MaximilianHq/bsc-thesis-agv-autonomous-parking/AGV/AGV CODE/src/MCU1/lift.h

#pragma once
#include <Arduino.h>
#include "system_actions.h"
#include <types.h>
#include <servo_continious.h>

class AGVCtrl;

class Lift
{
public:
    Lift(int pin_servo, int pin_begin_stop, int pin_endstop,
         int pwm_chnl, bool invert)
        : _servo(pin_servo, pwm_chnl, invert),
          _pin_begin_stop(pin_begin_stop),
          _pin_endstop(pin_endstop) {}

    void home()
    {
        if (g_debug.crane)
            Serial.println("[CRANE] Homing...");
        _is_moving = true;
        while (digitalRead(_pin_begin_stop) == LOW)
            _servo.drive_forward(100);
        _servo.stop();
        _is_moving = false;
        _is_homed = true;
        if (g_debug.crane)
            Serial.println("[CRANE] Hominging Complete");
    }

    void setup()
    {
        if (g_debug.crane)
            Serial.println("[CRANE] Running Setup...");

        _servo.setup();
        pinMode(_pin_begin_stop, INPUT);
        pinMode(_pin_endstop, INPUT);
        home();

        if (g_debug.crane)
            Serial.println("[CRANE] Setup Complete");
    }

    void update()
    {
        _servo.update();
        if (_is_moving)
        {
            if (digitalRead(_pin_endstop) == HIGH || digitalRead(_pin_begin_stop) == HIGH)
            {
                _is_moving = false;
                _servo.stop();

                if (g_debug.crane && digitalRead(_pin_endstop) == HIGH)
                    Serial.println("[CRANE] Endstop hit, stopping");

                if (g_debug.crane && digitalRead(_pin_begin_stop) == HIGH)
                    Serial.println("[CRANE] Contact with Car, stopping");

                *_rsv = true;
            }
        }
    }

    void lift(int8_t speed, bool &return_variable)
    {
        _rsv = &return_variable;
        _is_moving = true;
        _servo.drive_forward(speed);
    }

    void lower(int8_t speed, bool &return_variable)
    {
        _rsv = &return_variable;
        _is_moving = true;
        _servo.drive_backward(speed);
    }

    bool is_homed() { return _is_homed; }

private:
    bool *_rsv; // return status varaible pointer
    ServoContinious _servo;
    int _pin_endstop, _pin_begin_stop;
    bool _is_moving = false;
    bool _is_homed = false;
};
